AR1972/Xbox_tray_emulator/PCB/QSB 1.6/xbox_tray_emulator_bottom.png

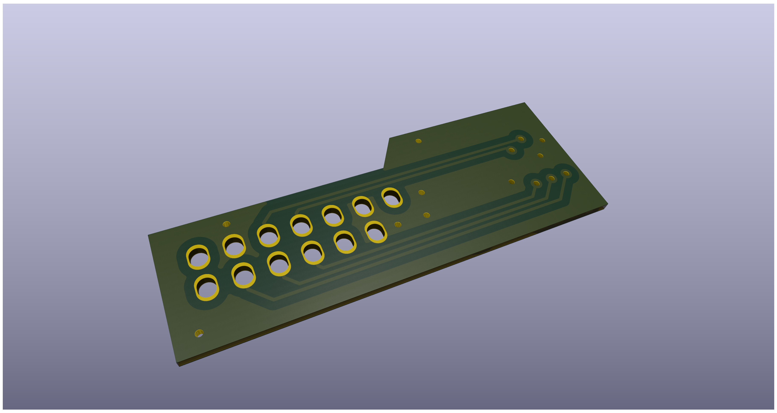
PCB/QSB 1.6/xbox_tray_emulator_bottom.png
